ssaunter/Oxide-S3/images/3dpcbfront.png

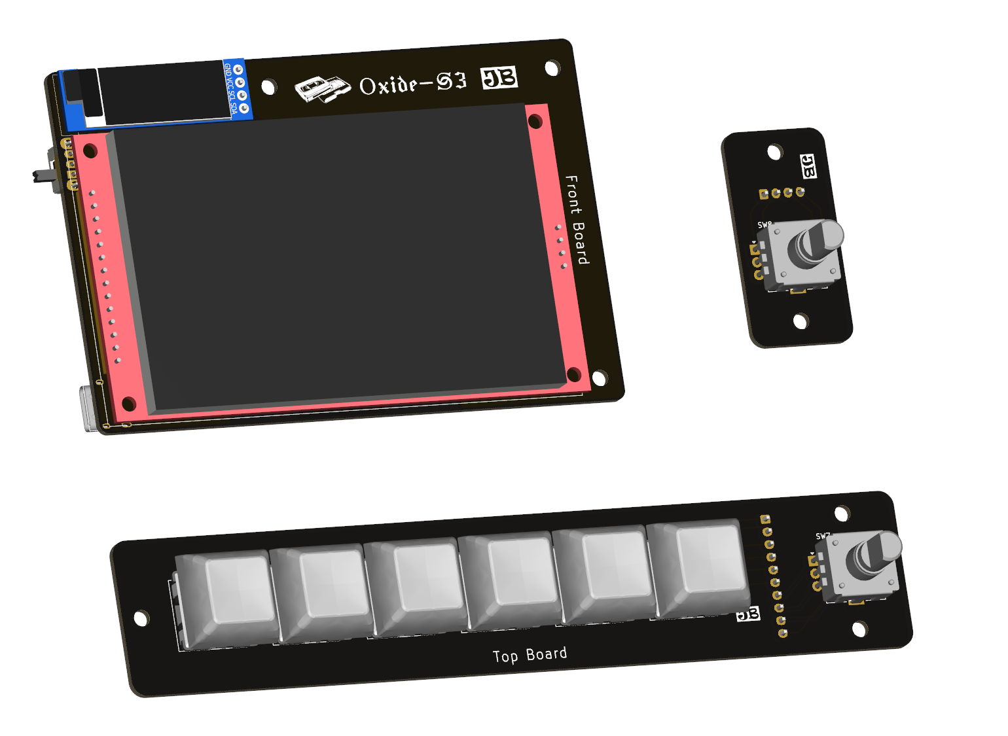
images/3dpcbfront.png
